PabloOyarzo/ESPlit/footprints/T-Display-S3/image11.jpg

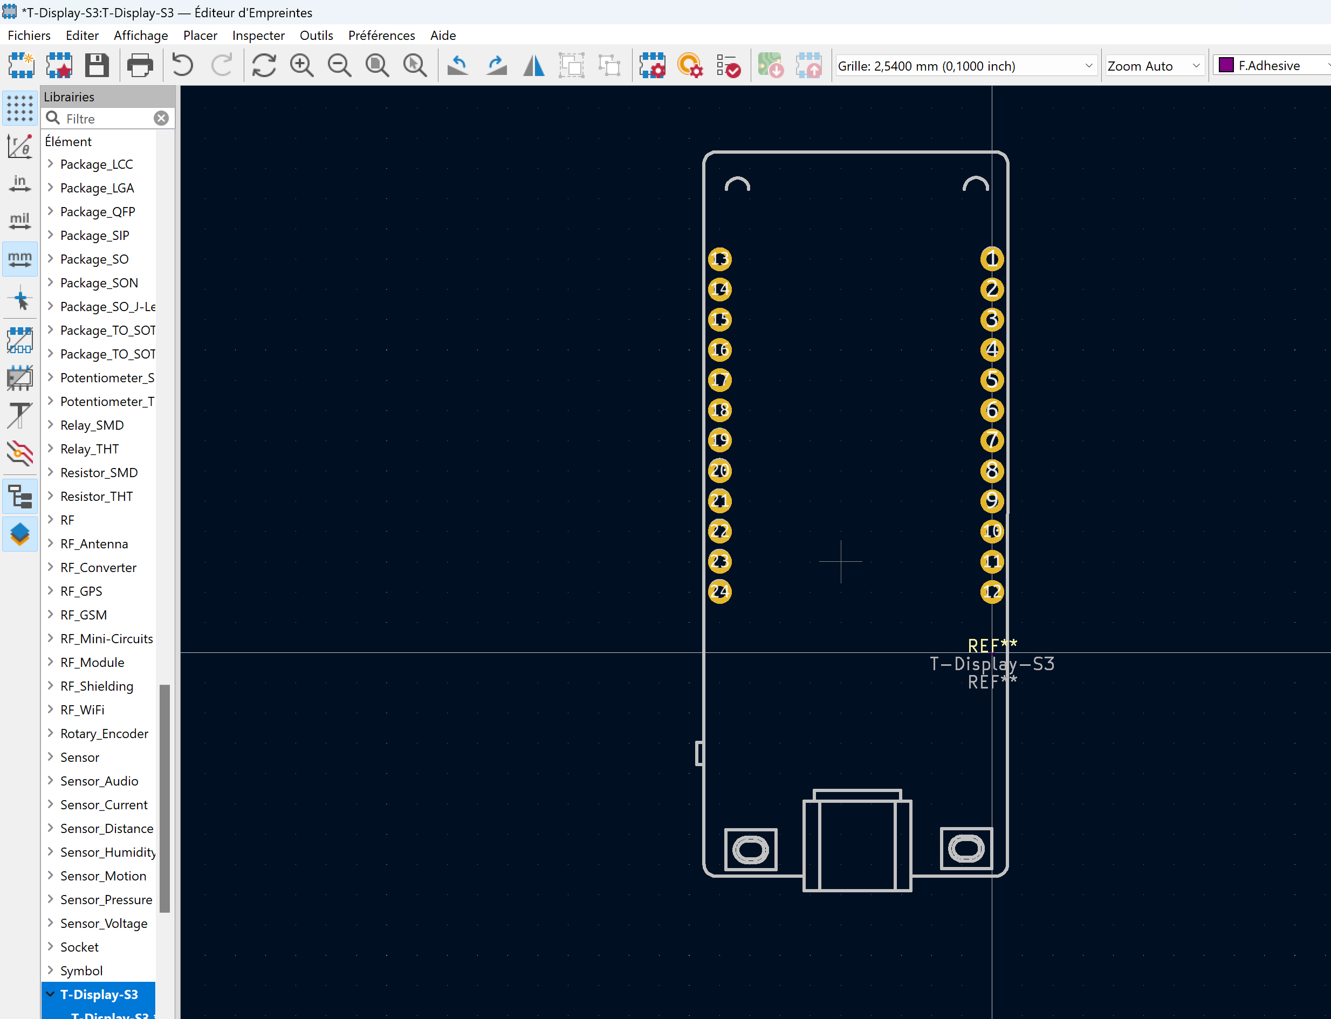
footprints/T-Display-S3/image11.jpg
